EddiZor/GreenTracker/images/001.jpeg

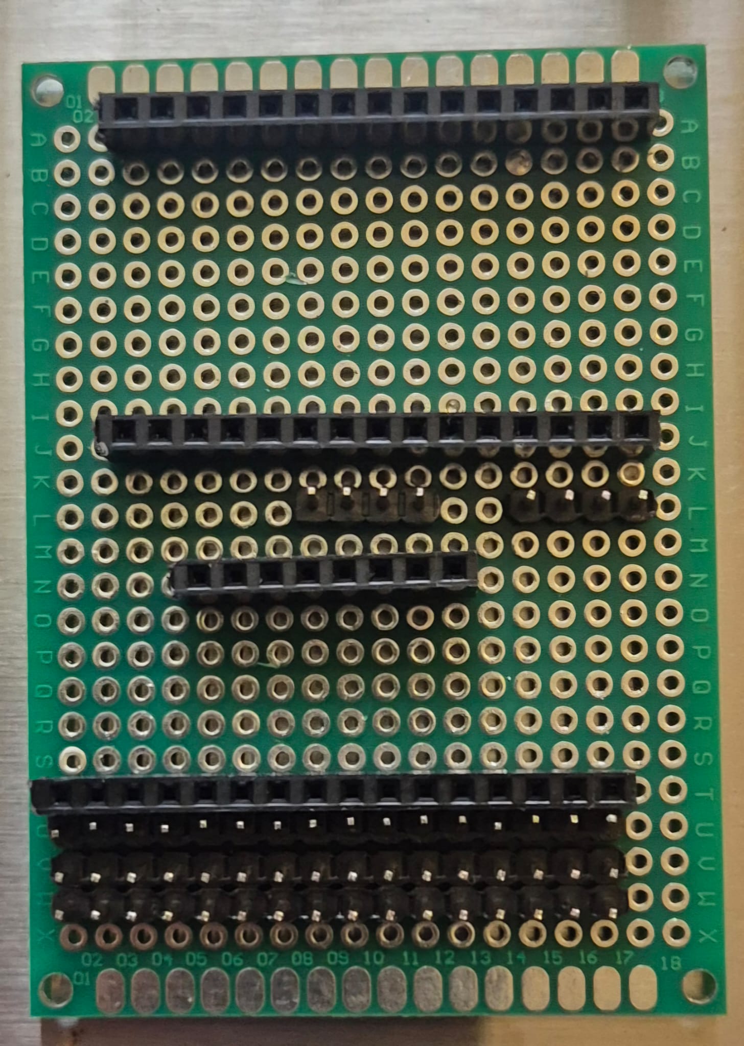
images/001.jpeg
