EddiZor/GreenTracker/images/003.jpeg

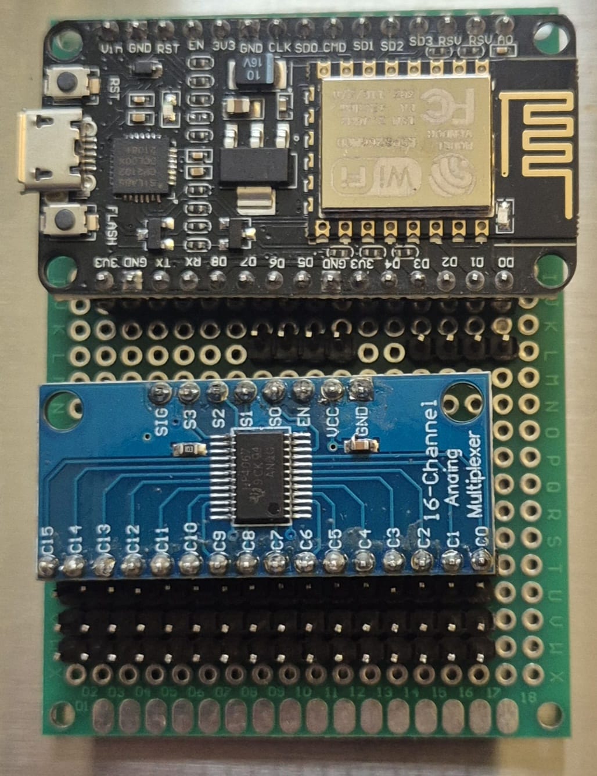
images/003.jpeg
