EddiZor/GreenTracker/WhatsApp Image 2026-09-13 at 14.47.45.jpeg

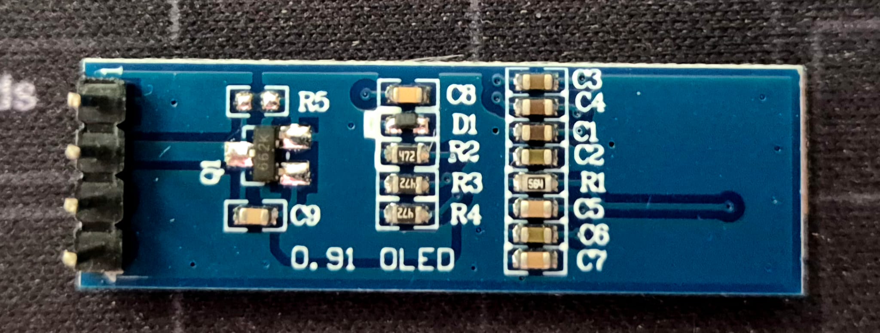
WhatsApp Image 2026-09-13 at 14.47.45.jpeg
